unixjazz/transcriba/transcriba.py

#! /usr/bin/python
#
# Pedal Transcriba 0.5
# VLC-based multimedia player for the using w/ an USB pedal.
# Based on the PyQt VLC player, created by the VideoLAN team.
#
# Copyright (C) 2009-2010 the VideoLAN team
# Copyright (C) 2017 unixjazz
#
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
import os
import re
import sys
import user
import vlc
from evdev import InputDevice
from PyQt4 import QtGui, QtCore

# use autofind 
pedaldev = InputDevice('/dev/input/event11')

if pedaldev:
   print('Pedal device found!')
else:
   print('Pedal device not found. Is it connected?')

# audio/video player
class Player(QtGui.QMainWindow):
   def __init__(self, master=None):
      QtGui.QMainWindow.__init__(self, master)
      self.setWindowTitle("Pedal Transcriba")
      # creating a basic vlc instance
      self.Instance = vlc.Instance()
      # creating an empty vlc media player
      self.MediaPlayer = self.Instance.media_player_new()
      
      self.createUI()
      self.isPaused = False

   def createUI(self):
      self.Widget = QtGui.QWidget(self)
      self.setCentralWidget(self.Widget)

      # In this widget, the video will be drawn
      self.VideoFrame = QtGui.QFrame()
      self.Palette = self.VideoFrame.palette()
      self.Palette.setColor (QtGui.QPalette.Window,
                             QtGui.QColor(128,128,128))
      self.VideoFrame.setPalette(self.Palette)
      self.VideoFrame.setAutoFillBackground(True)

      self.PositionSlider = QtGui.QSlider(QtCore.Qt.Horizontal, self)
      self.PositionSlider.setToolTip("Position")
      self.PositionSlider.setMaximum(1000)
      self.connect(self.PositionSlider,
                   QtCore.SIGNAL("sliderMoved(int)"), self.setPosition)

      self.HButtonBox = QtGui.QHBoxLayout()
      self.LoadButton = QtGui.QPushButton("Load File")
      self.HButtonBox.addWidget(self.LoadButton)
      self.connect(self.LoadButton, QtCore.SIGNAL("clicked()"),
                   self.OpenFile)
       
      self.PlayButton = QtGui.QPushButton("Play")
      self.HButtonBox.addWidget(self.PlayButton)
      self.connect(self.PlayButton, QtCore.SIGNAL("clicked()"),
                   self.PlayPause)

      self.StopButton = QtGui.QPushButton("Stop")
      self.HButtonBox.addWidget(self.StopButton)
      self.connect(self.StopButton, QtCore.SIGNAL("clicked()"),
                   self.Stop)

      self.BWButton = QtGui.QPushButton("<<")
      self.HButtonBox.addWidget(self.BWButton)
      self.connect(self.BWButton, QtCore.SIGNAL("clicked()"),
                   self.Back5)

      self.FWButton = QtGui.QPushButton(">>")
      self.HButtonBox.addWidget(self.FWButton)
      self.connect(self.FWButton, QtCore.SIGNAL("clicked()"),
                   self.Jump5)
      
      self.PitchUpButton = QtGui.QPushButton("Pitch Up")
      self.HButtonBox.addWidget(self.PitchUpButton)
      self.connect(self.PitchUpButton, QtCore.SIGNAL("clicked()"),
                   self.PitchUp)

      self.PitchDownButton = QtGui.QPushButton("Pitch Down")
      self.HButtonBox.addWidget(self.PitchDownButton)
      self.connect(self.PitchDownButton, QtCore.SIGNAL("clicked()"),
                   self.PitchDown)

      self.TimecodeButton = QtGui.QPushButton("Timecode")
      self.HButtonBox.addWidget(self.TimecodeButton)
      self.connect(self.TimecodeButton, QtCore.SIGNAL("clicked()"),
                   self.Timecode)
 
      self.HButtonBox.addStretch(1)
      self.VolumeSlider = QtGui.QSlider(QtCore.Qt.Horizontal, self)
      self.VolumeSlider.setMaximum(100)
      self.VolumeSlider.setValue(self.MediaPlayer.audio_get_volume())
      self.VolumeSlider.setToolTip("Volume")
      self.HButtonBox.addWidget(self.VolumeSlider)
      self.connect(self.VolumeSlider,
                   QtCore.SIGNAL("valueChanged(int)"), self.setVolume)

      self.VBoxLayout = QtGui.QVBoxLayout()
      self.VBoxLayout.addWidget(self.VideoFrame)
      self.VBoxLayout.addWidget(self.PositionSlider)
      self.VBoxLayout.addLayout(self.HButtonBox)

      self.Widget.setLayout(self.VBoxLayout)

      self.Timer = QtCore.QTimer(self)
      self.Timer.setInterval(200)
      self.connect(self.Timer, QtCore.SIGNAL("timeout()"),
                   self.updateUI)

   def PlayPause(self):
      if self.MediaPlayer.is_playing():
         self.MediaPlayer.pause()
         self.PlayButton.setText("Play")
         self.isPaused = True
      else:
         if self.MediaPlayer.play() == -1:
            self.OpenFile()
            return
            self.MediaPlayer.play()
            self.PlayButton.setText("Pause")
            self.Timer.start()
            self.isPaused = False

   def Stop(self):
      self.MediaPlayer.stop()
      self.PlayButton.setText("Play")
   
   def Back5(self):
      self.MediaPlayer.set_time(self.MediaPlayer.get_time() - 5000)

   def Jump5(self):
      self.MediaPlayer.set_time(self.MediaPlayer.get_time() + 5000)
   
   def PitchDown(self):
      self.MediaPlayer.set_rate(self.MediaPlayer.get_rate() - 0.10)
      print(self.MediaPlayer.get_rate())

   def PitchUp(self):
      self.MediaPlayer.set_rate(self.MediaPlayer.get_rate() + 0.10)
      print(self.MediaPlayer.get_rate())
   
   def Timecode(self):
      match_seconds = re.compile(r"^0*[1-9][0-9]*")
      milisec = self.MediaPlayer.get_time()
      th = milisec / 60 / 1000
      tm = milisec % (60 * 1000) / 1000
      ts = milisec % 1000
      timecode = "%02d:%02d:%02d" % (th,tm,ts)
      timecode = "[" + timecode + "] "
      print "Timecode: %s" % timecode
      clipboard.setText(timecode)
   
   def OpenFile(self):
      filename = QtGui.QFileDialog.getOpenFileName(self,
                                                   "Open File", user.home)
      if not filename:
         return

      # create the media
      self.Media = self.Instance.media_new(unicode(filename))
      # put the media in the media player
      self.MediaPlayer.set_media(self.Media)

      # parse the metadata of the file
      self.Media.parse()
      # set the title of the track as window title
      self.setWindowTitle(self.Media.get_meta(0))

      # the media player has to be 'connected' to the QFrame
      # (otherwise a video would be displayed in it's own window)
      # this is platform specific!
      # you have to give the id of the QFrame (or similar object) to
      # vlc, different platforms have different functions for this
      if sys.platform == "linux2": # for Linux using the X Server
          self.MediaPlayer.set_xwindow(self.VideoFrame.winId())
      elif sys.platform == "win32": # for Windows
          self.MediaPlayer.set_hwnd(self.VideoFrame.winId())
      elif sys.platform == "darwin": # for MacOS
          self.MediaPlayer.set_agl(self.VideoFrame.windId())
      self.PlayPause()

   def setVolume(self, Volume):
      self.MediaPlayer.audio_set_volume(Volume)

   def setPosition(self, Position):
      # setting the position to where the slider was dragged
      self.MediaPlayer.set_position(Position / 1000.0)
      # the vlc MediaPlayer needs a float value between 0 and 1, Qt
      # uses integer variables, so you need a factor; the higher the
      # factor, the more precise are the results
      # (1000 should be enough)

   def pedalbuttonRead(self, event):
      for event in pedaldev.read_loop():    
         if event.code == 288:
            PitchUp()
         elif event.code == 289:
            PitchDown()
         elif event.code == 290:
            Jump5()
      
   def updateUI(self):
      # setting the slider to the desired position
      self.PositionSlider.setValue(self.MediaPlayer.get_position() * 1000)

      if not self.MediaPlayer.is_playing():
          # no need to call this function if nothing is played
          self.Timer.stop()
          if not self.isPaused:
              # after the video finished, the play button stills shows
              # "Pause", not the desired behavior of a media player
              # this will fix it
              self.Stop()
      
      if pedaldev is None:
          self.PedalStatus.setValue()
          

if __name__ == "__main__":
   app = QtGui.QApplication(sys.argv)
   clipboard = app.clipboard()
   MediaPlayer = Player()
   MediaPlayer.show()
   MediaPlayer.resize(720, 480)
   sys.exit(app.exec_())
